74th/sparrow62-buildguide/img/60c/sparrow60c_default_keymap.png

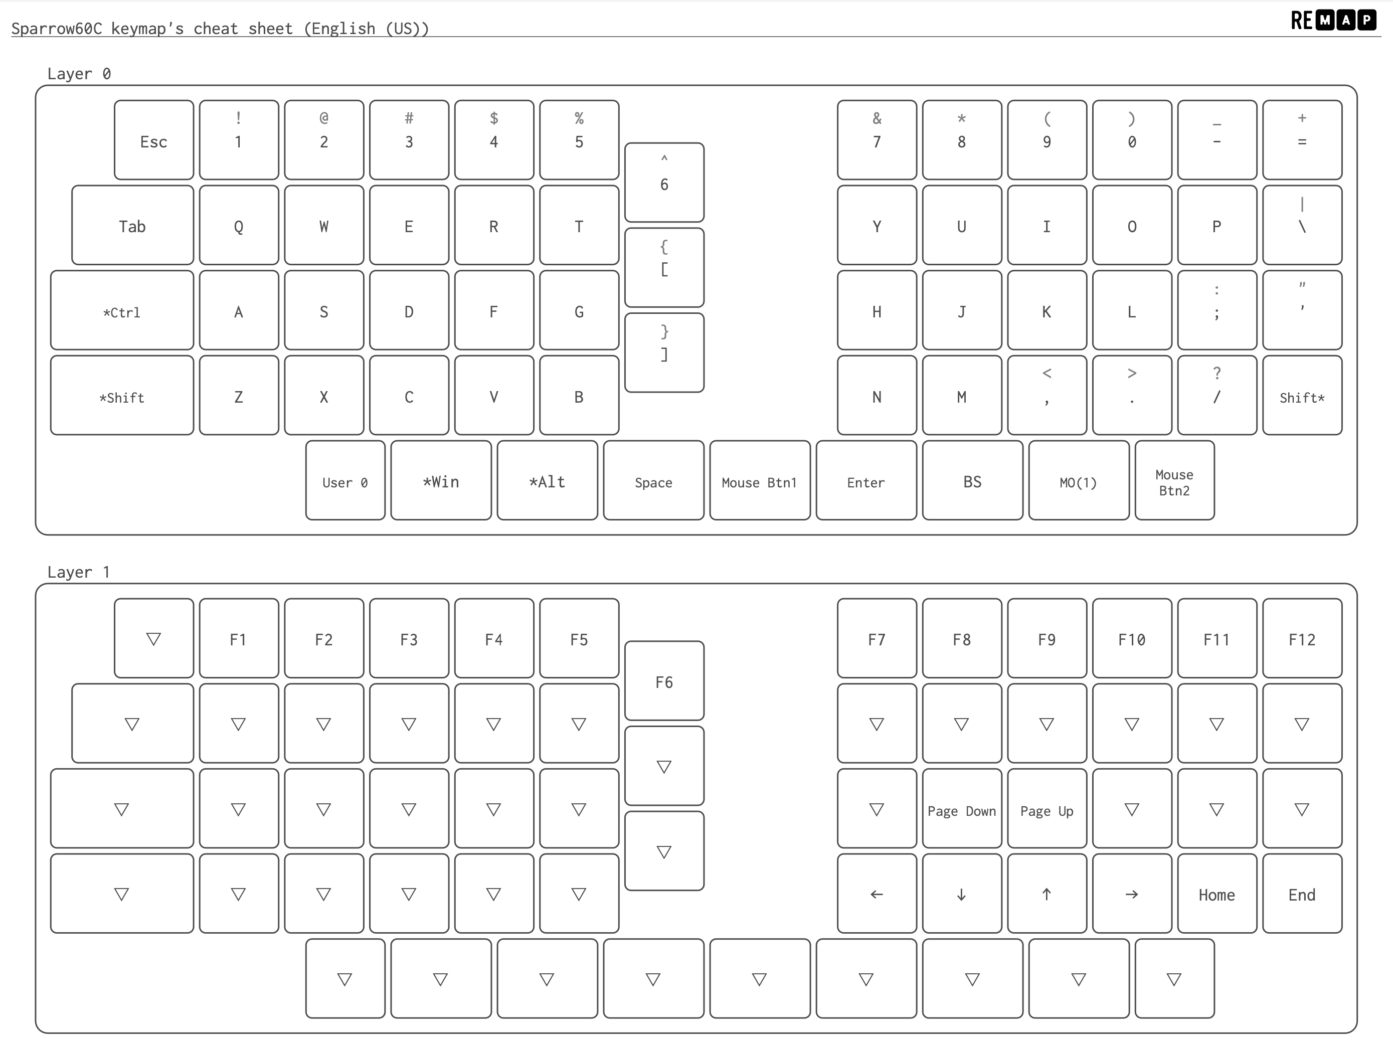
img/60c/sparrow60c_default_keymap.png
