74th/sparrow62-buildguide/img/62v1/diode3.jpg

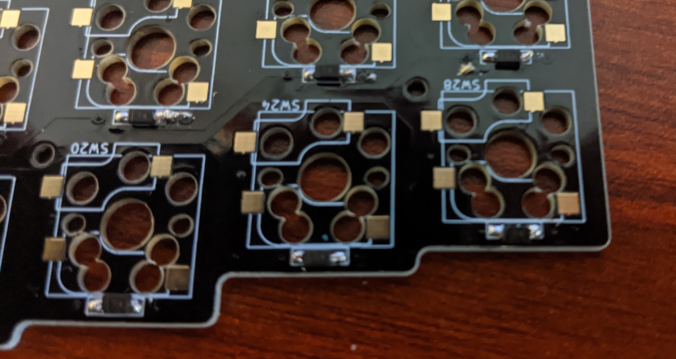
img/62v1/diode3.jpg
