74th/sparrow62-buildguide/img/62v1/keymap_default.png

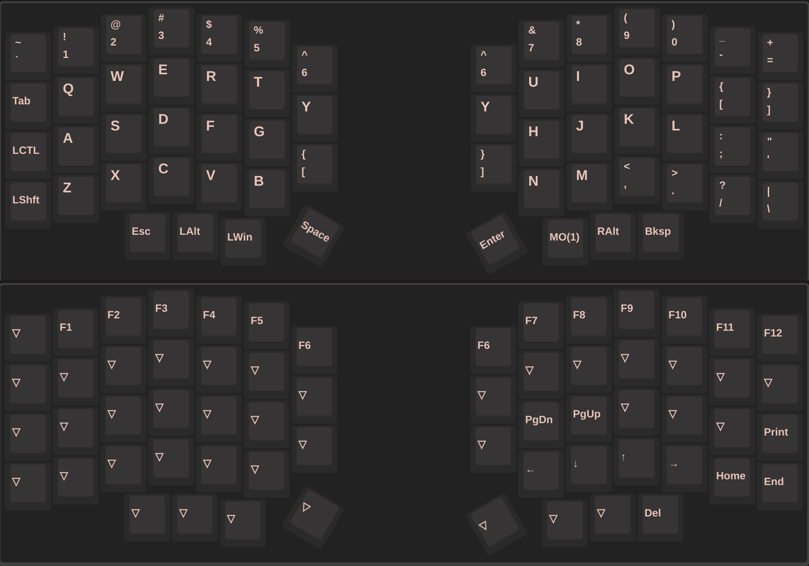
img/62v1/keymap_default.png
