74th/sparrow62-buildguide/img/62v1/pcb.jpg

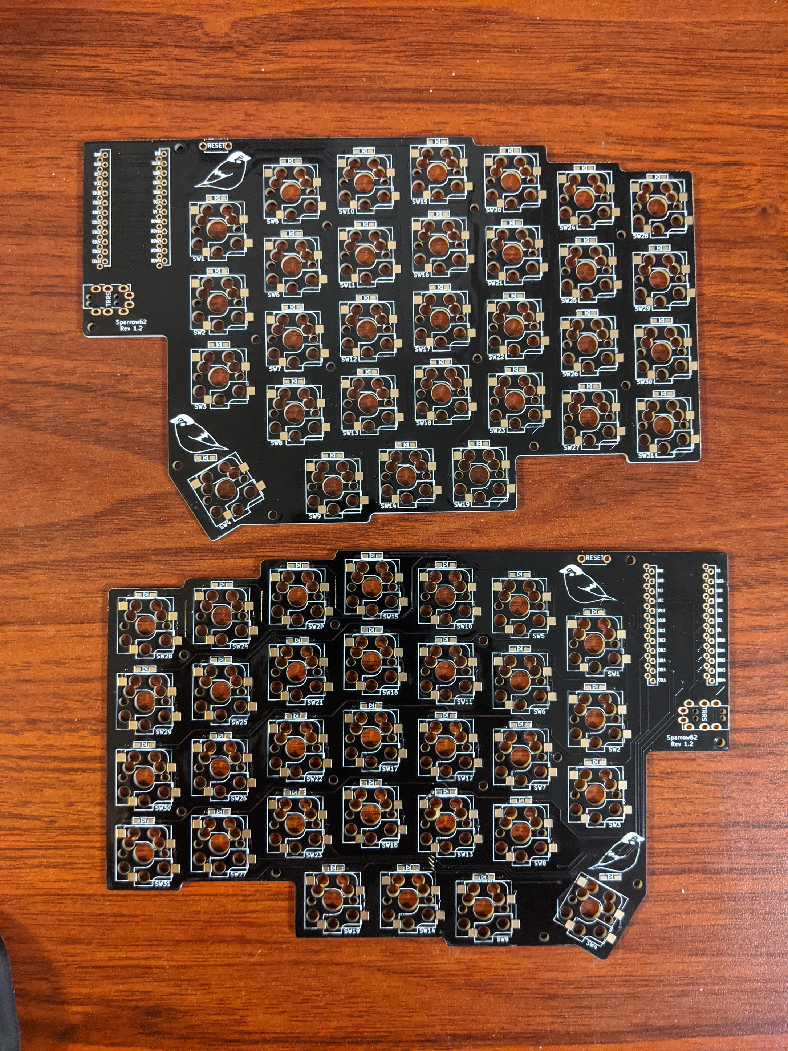
img/62v1/pcb.jpg
