74th/sparrow62-buildguide/img/62v1/top_choc3.jpg

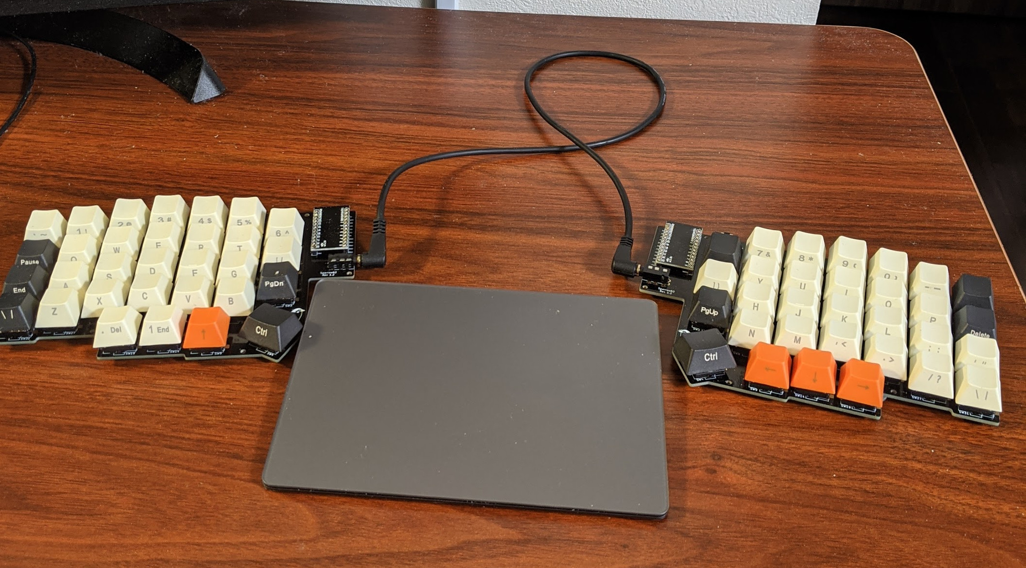
img/62v1/top_choc3.jpg
