74th/sparrow62-buildguide/img/62v1/trackpad.jpeg

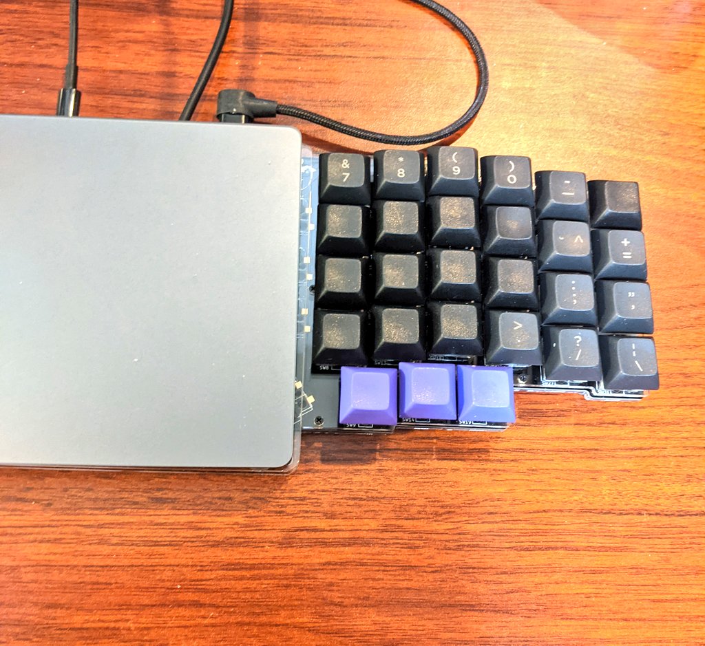
img/62v1/trackpad.jpeg
