74th/sparrow62-buildguide/img/62v2/diode_2.jpg

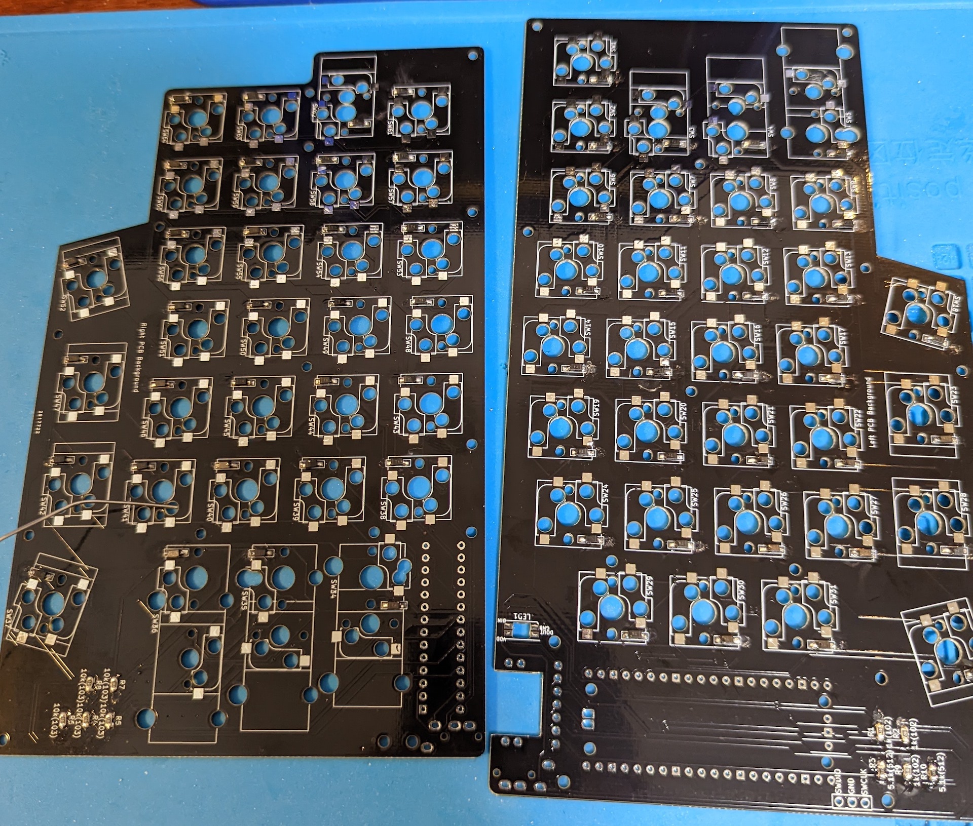
img/62v2/diode_2.jpg
