74th/sparrow62-buildguide/img/62v2/trackpad_option.jpg

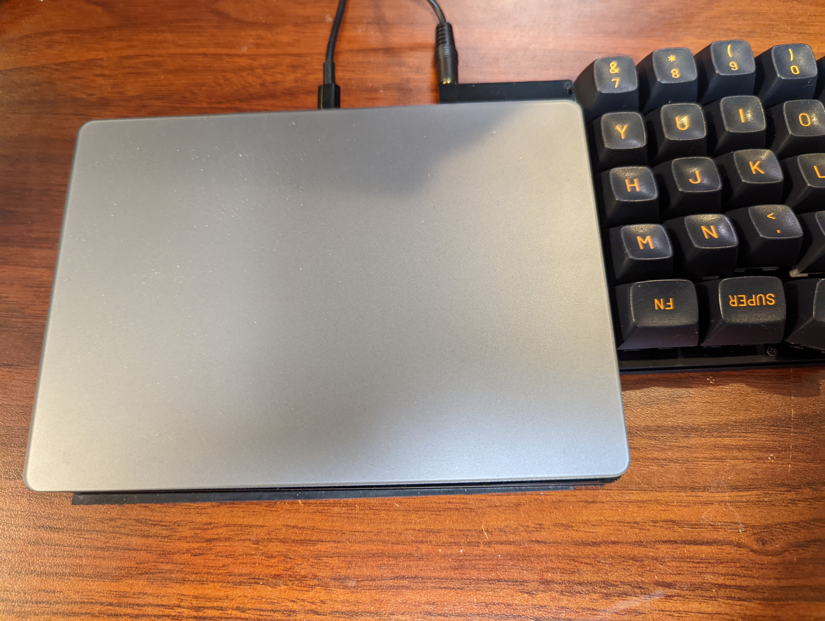
img/62v2/trackpad_option.jpg
