74th/sparrow62-buildguide/img/common/remap_select_usb.png

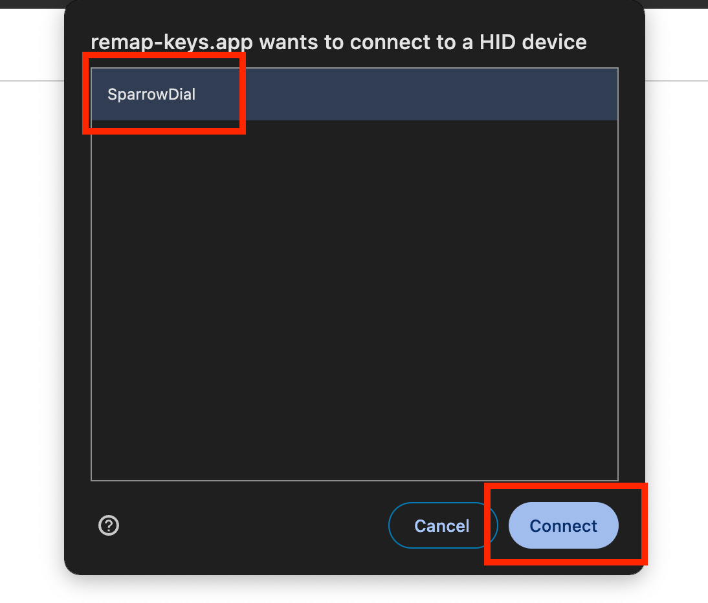
img/common/remap_select_usb.png
