74th/sparrow62-buildguide/img/dial/sparrowdial_default_keymap.png

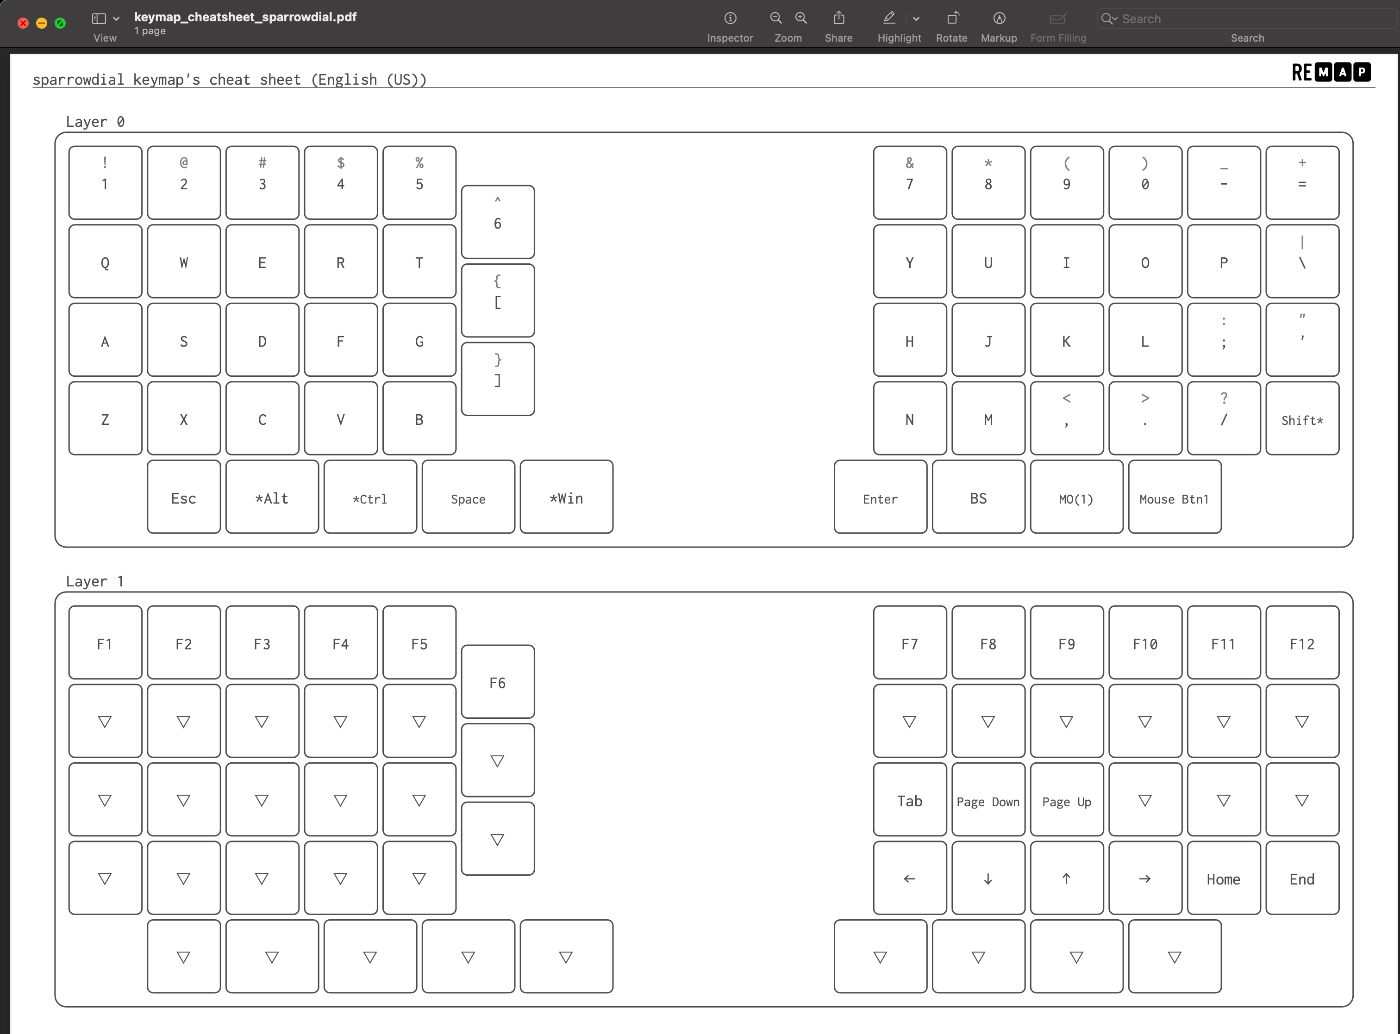
img/dial/sparrowdial_default_keymap.png
