74th/sparrow62-buildguide/img/g21/gp2040-peripheral-mapping.png

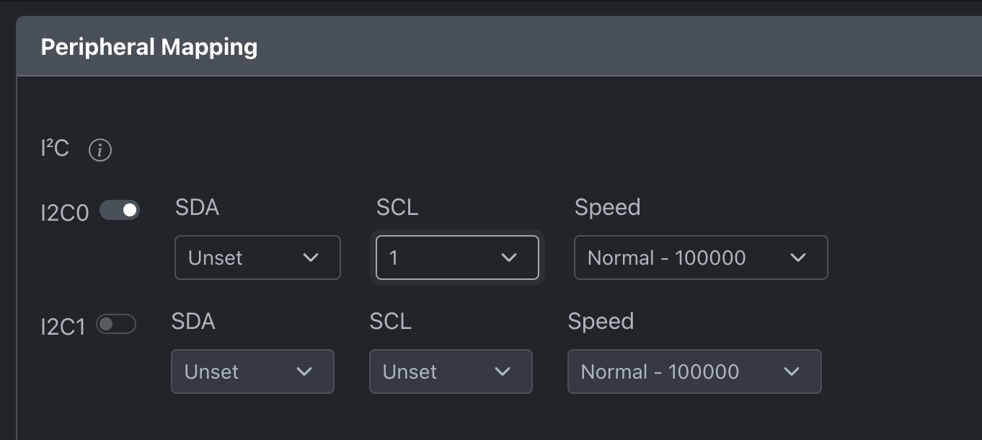
img/g21/gp2040-peripheral-mapping.png
