74th/sparrow62-buildguide/img/g21/gp2040-pin-mapping-v0.7.7.png

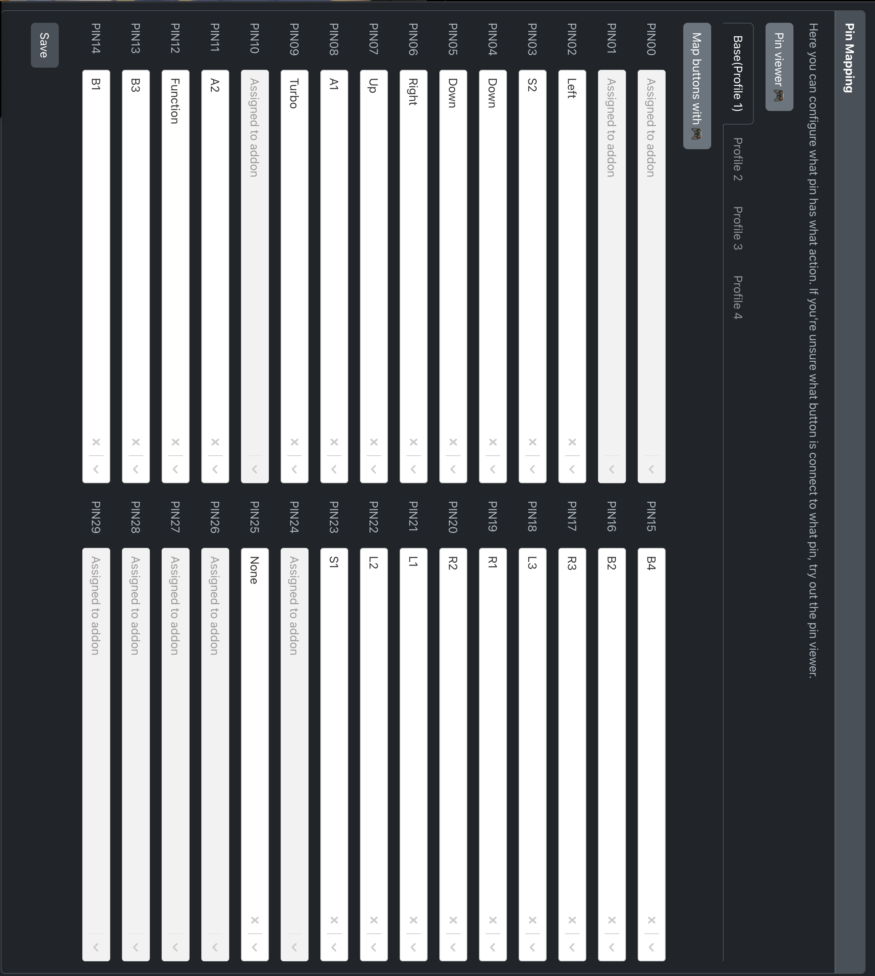
img/g21/gp2040-pin-mapping-v0.7.7.png
