74th/sparrow62-buildguide/img/g21/gp2040-turbo.png

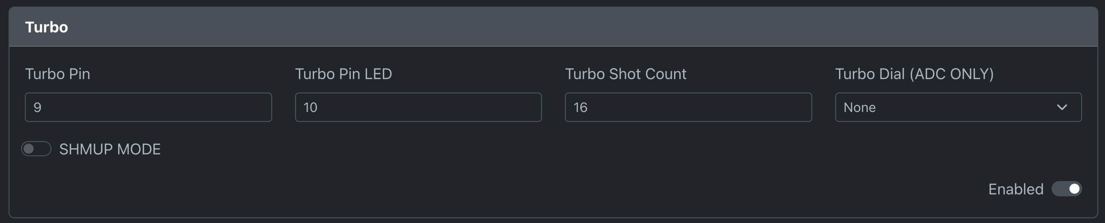
img/g21/gp2040-turbo.png
