74th/sparrow62-buildguide/photos/60c/alminium_case.jpg

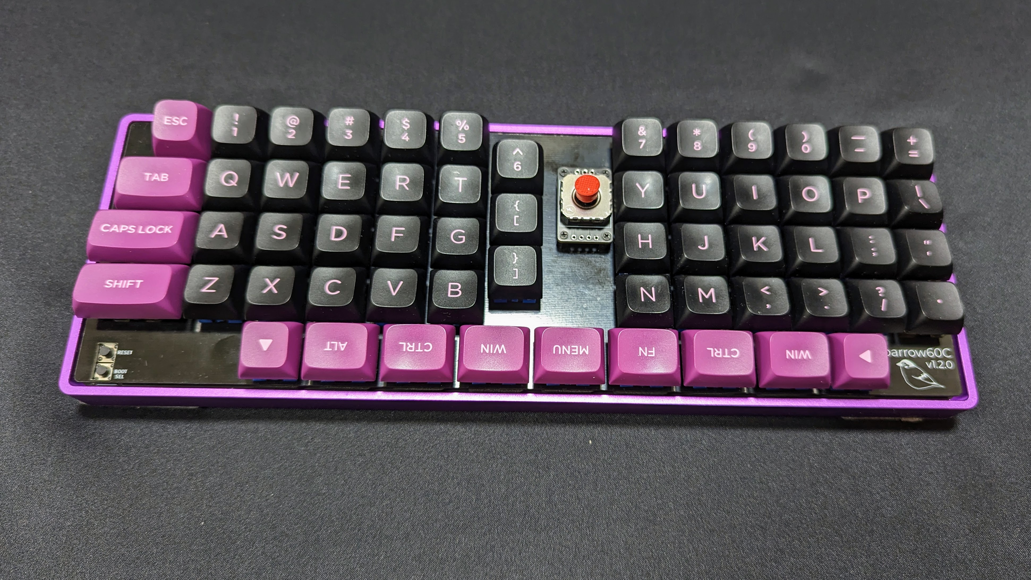
photos/60c/alminium_case.jpg
