74th/sparrow62-buildguide/photos/60c/slide.png

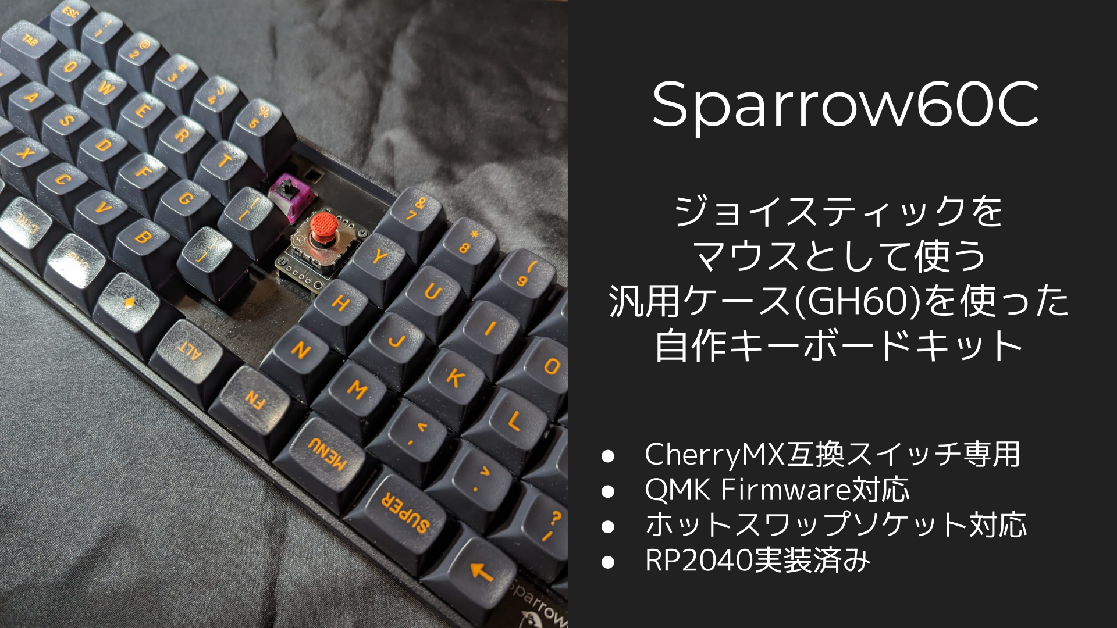
photos/60c/slide.png
