74th/sparrow62-buildguide/photos/60c/stick.jpg

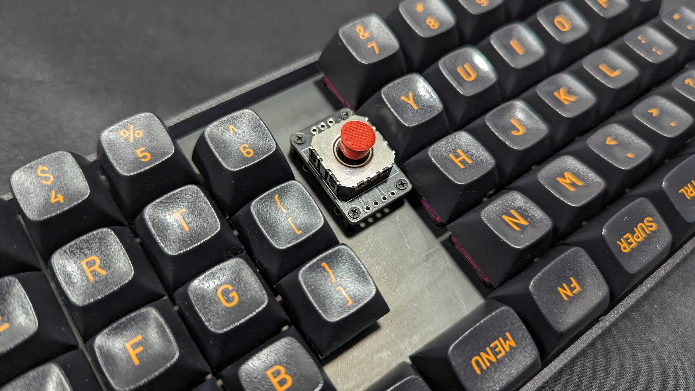
photos/60c/stick.jpg
