74th/sparrow62-buildguide/photos/dial/dial2.jpg

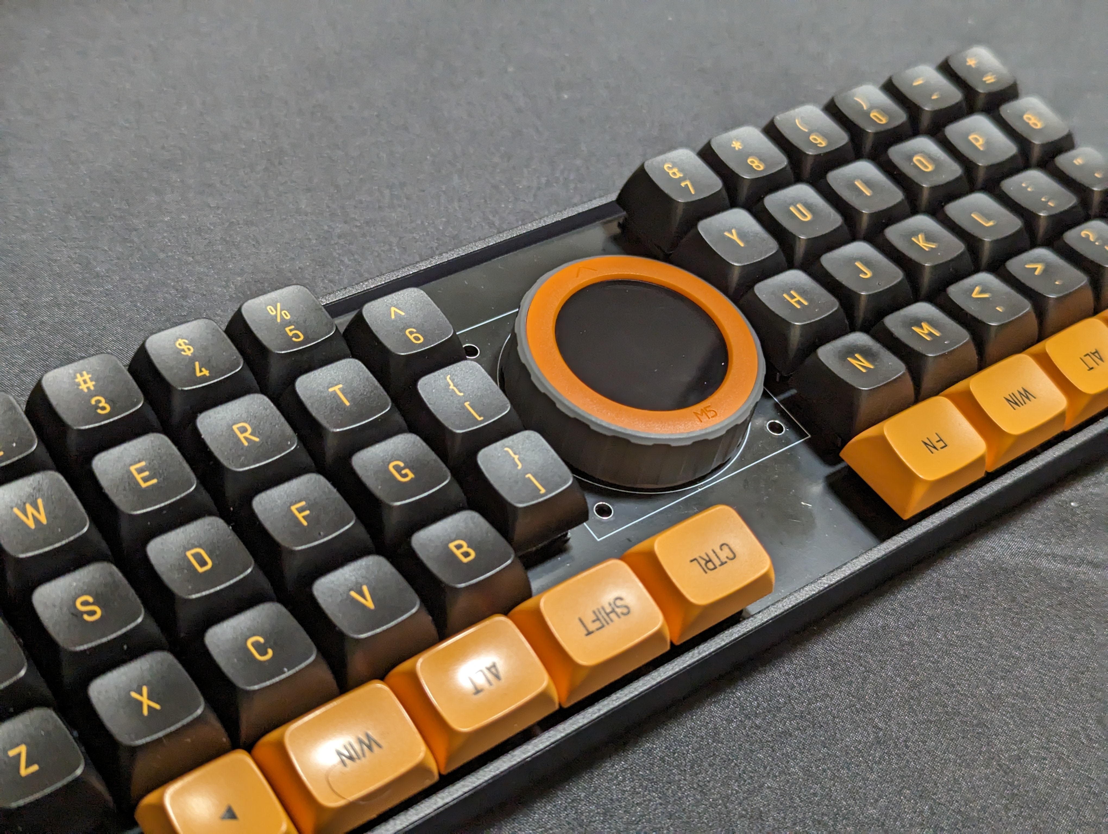
photos/dial/dial2.jpg
