74th/sparrow62-buildguide/photos/dial/dial.jpg

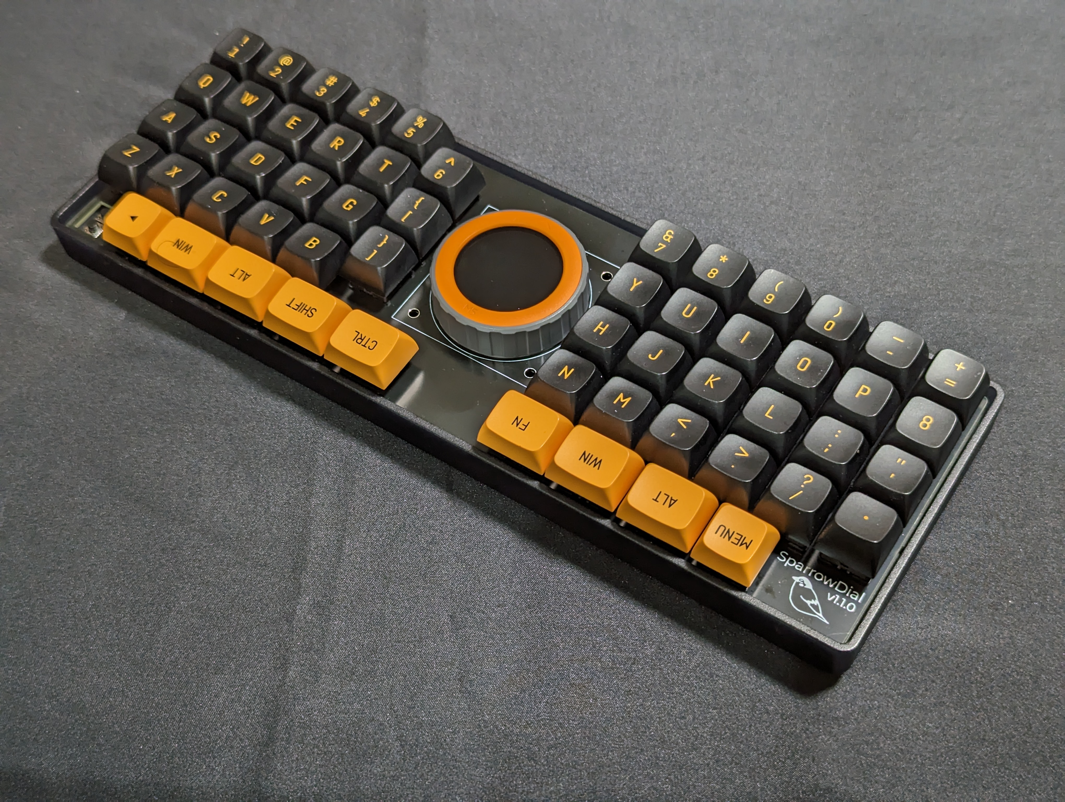
photos/dial/dial.jpg
