74th/sparrow62-buildguide/photos/dial/double.jpg

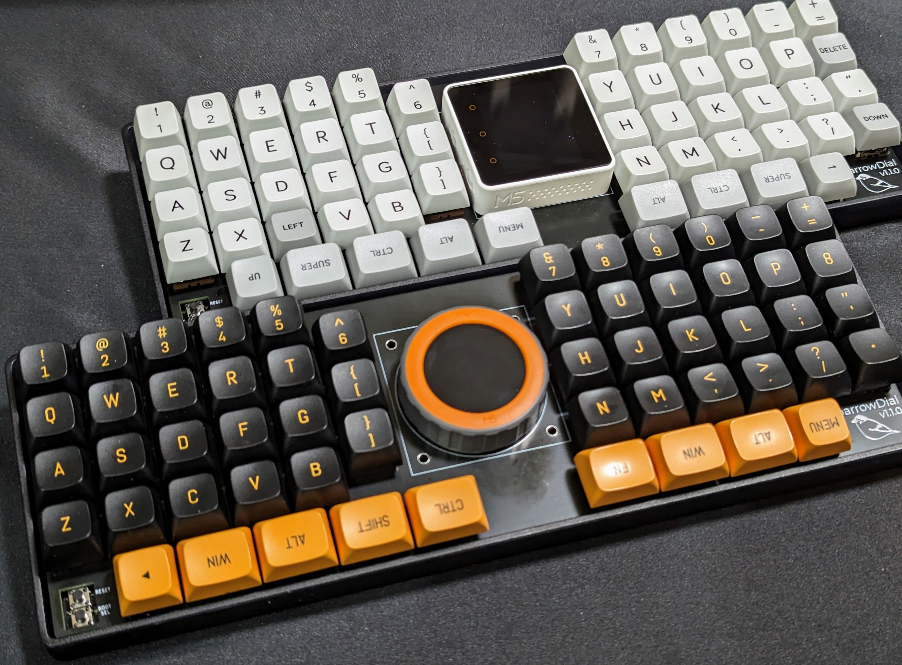
photos/dial/double.jpg
