74th/sparrow62-buildguide/photos/dial/stack2.jpg

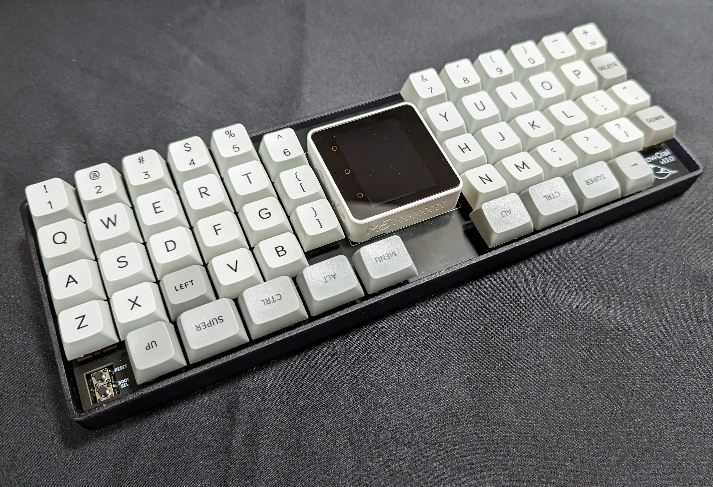
photos/dial/stack2.jpg
