74th/sparrow62-buildguide/photos/dial/stack.jpg

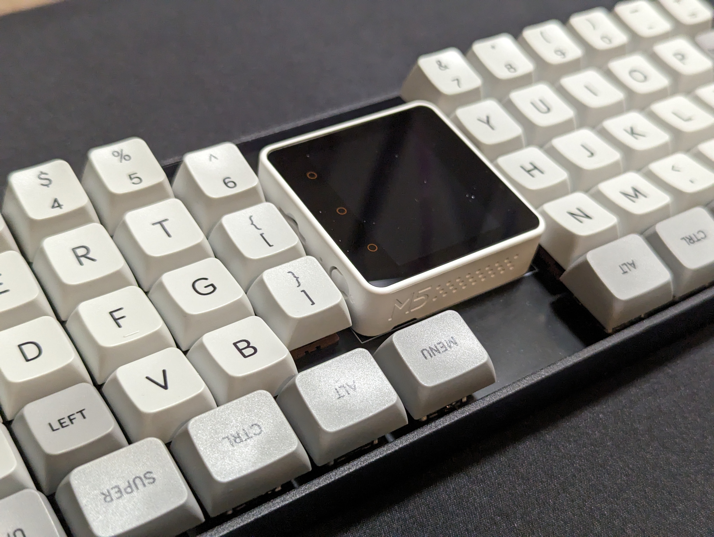
photos/dial/stack.jpg
