74th/sparrow62-buildguide/photos/g21/hollowknight.png

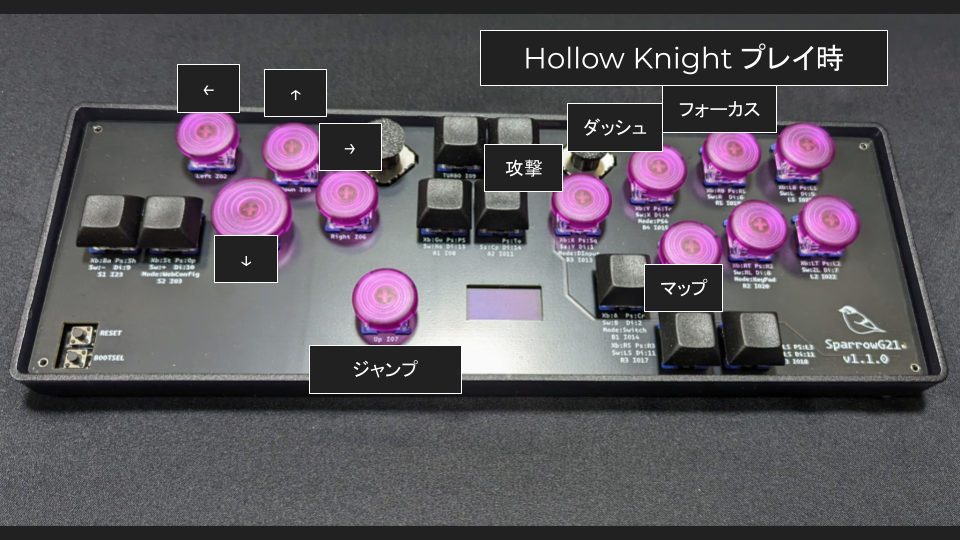
photos/g21/hollowknight.png
