74th/sparrow62-buildguide/photos/g21/joystick.jpg

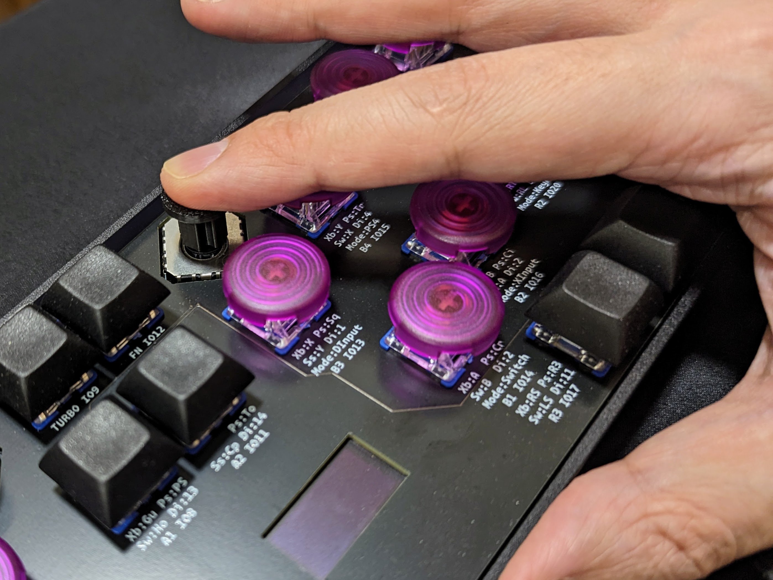
photos/g21/joystick.jpg
