74th/sparrow62-buildguide/photos/g21/left.jpg

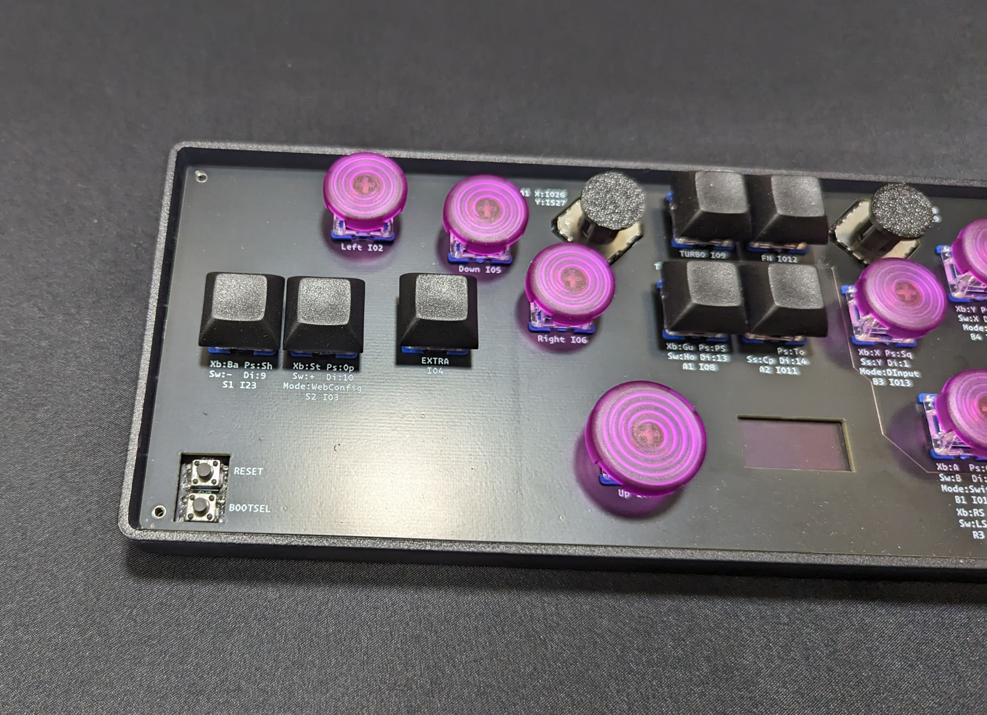
photos/g21/left.jpg
