74th/sparrow62-buildguide/photos/g21/overview.jpg

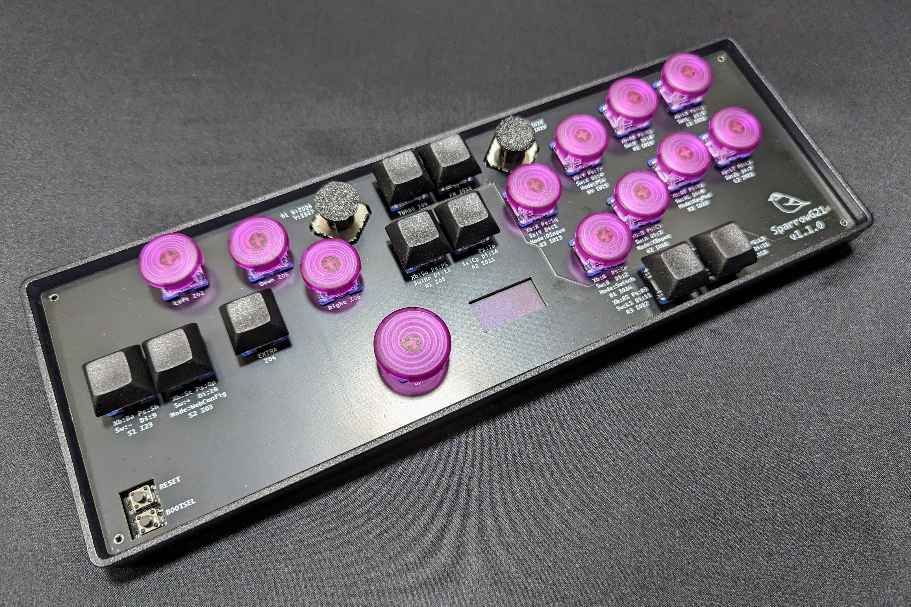
photos/g21/overview.jpg
