74th/sparrow62-buildguide/photos/g21/right.jpg

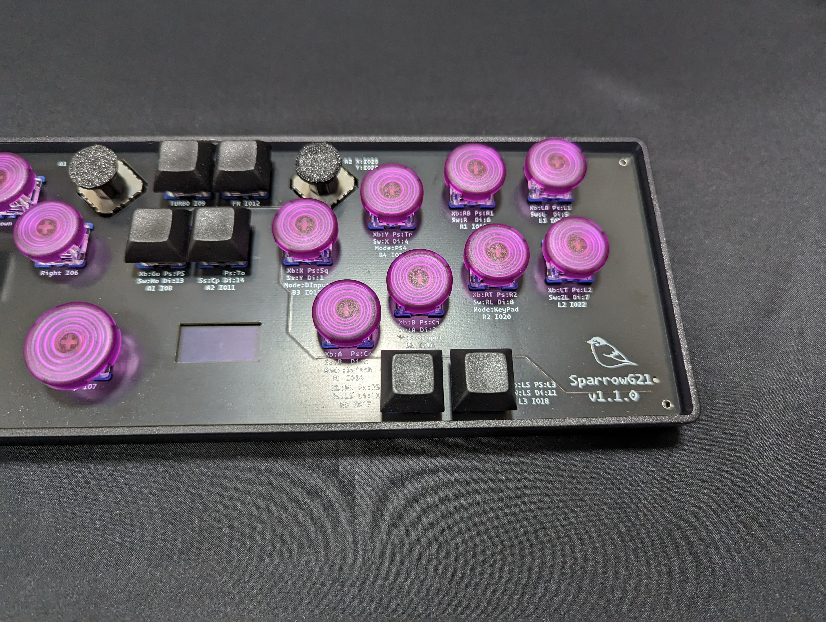
photos/g21/right.jpg
