74th/sparrow62-buildguide/photos/g21/slide.png

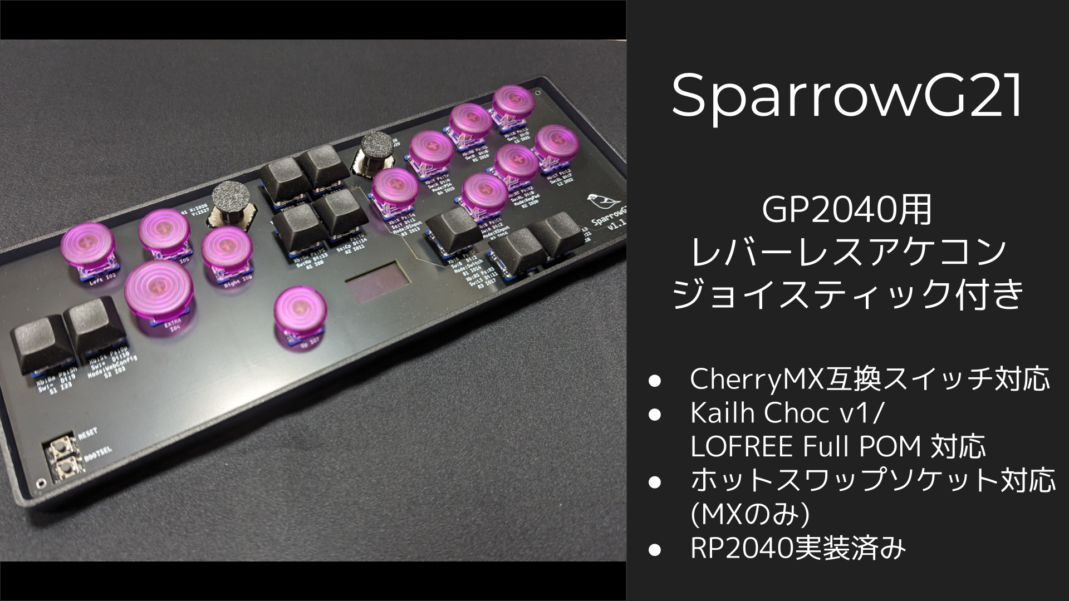
photos/g21/slide.png
