74th/sparrow62-buildguide/photos/tv/top.jpg

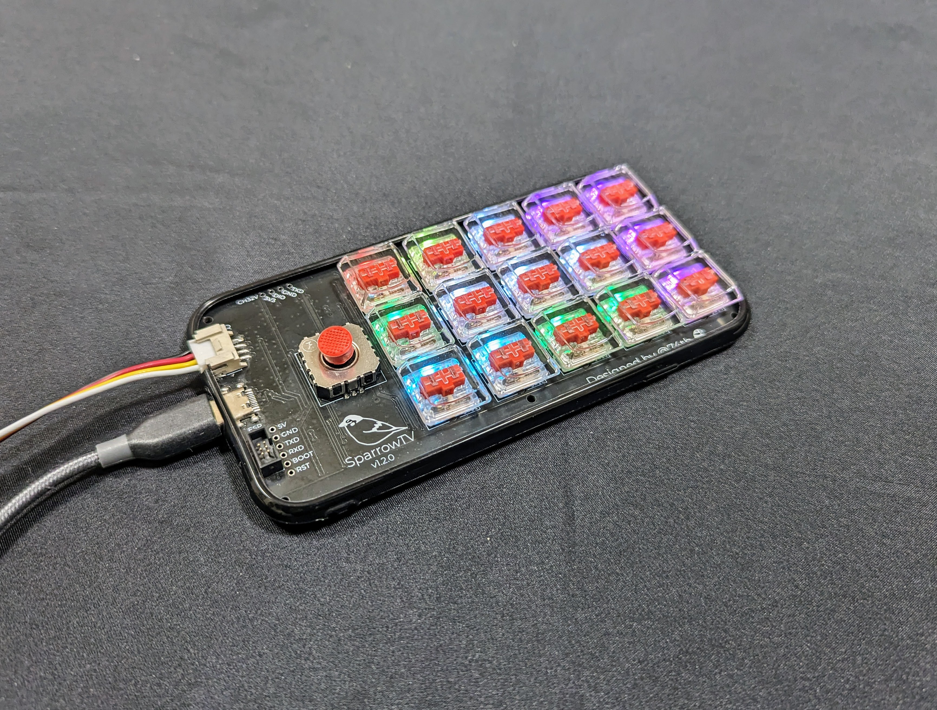
photos/tv/top.jpg
