74th/sparrow62-buildguide/photos/v2/left.jpg

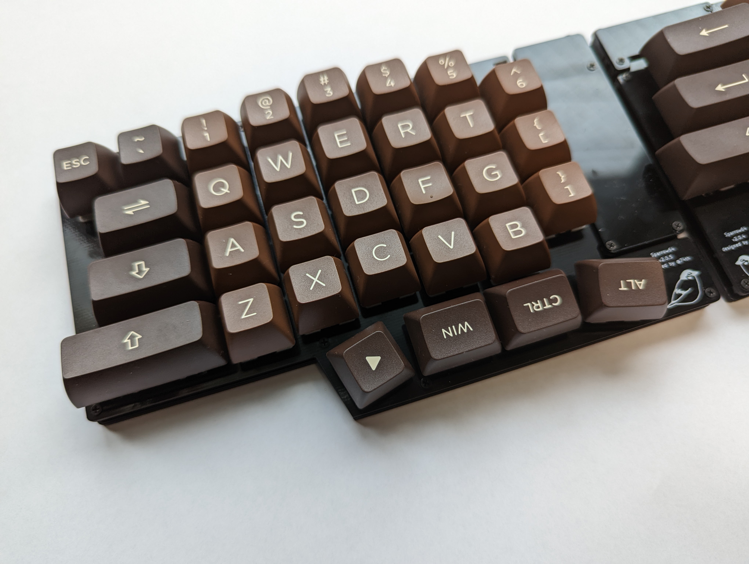
photos/v2/left.jpg
