74th/sparrow62-buildguide/photos/v2/lower.png

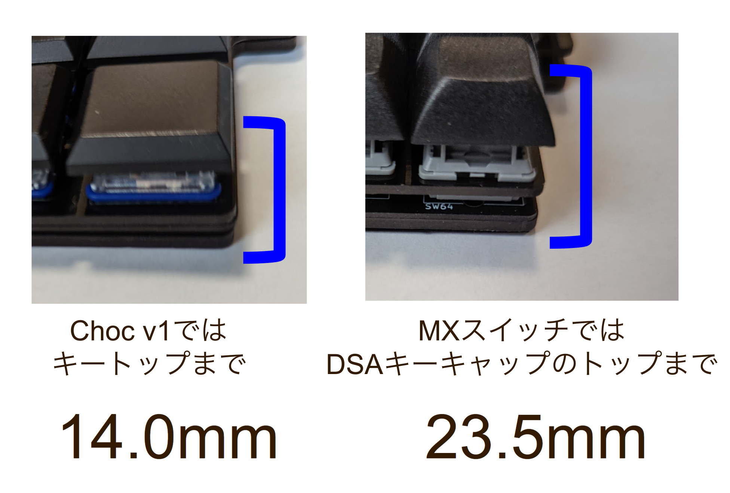
photos/v2/lower.png
