74th/sparrow62-buildguide/photos/v2/plate-back.jpg

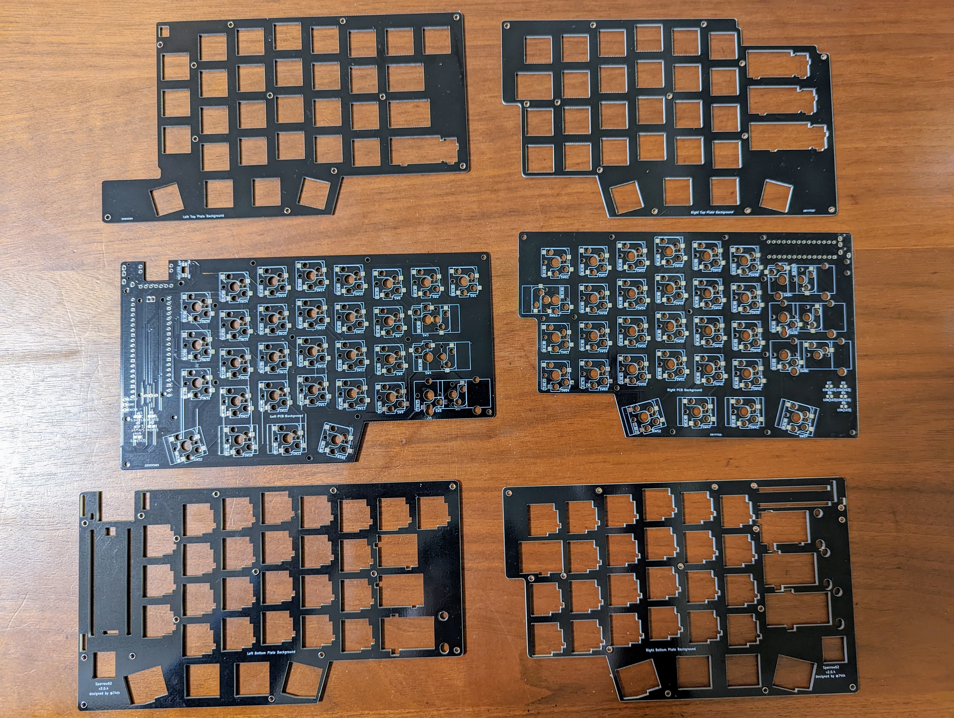
photos/v2/plate-back.jpg
