74th/sparrow62-buildguide/photos/v2/plate-front.jpg

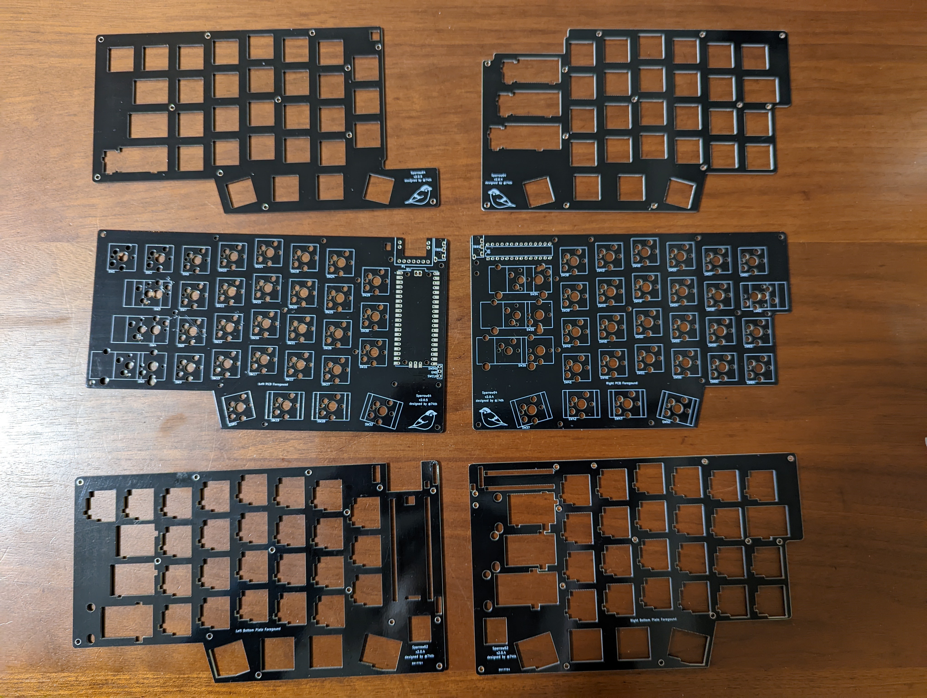
photos/v2/plate-front.jpg
