74th/sparrow62-buildguide/photos/v2/right.jpg

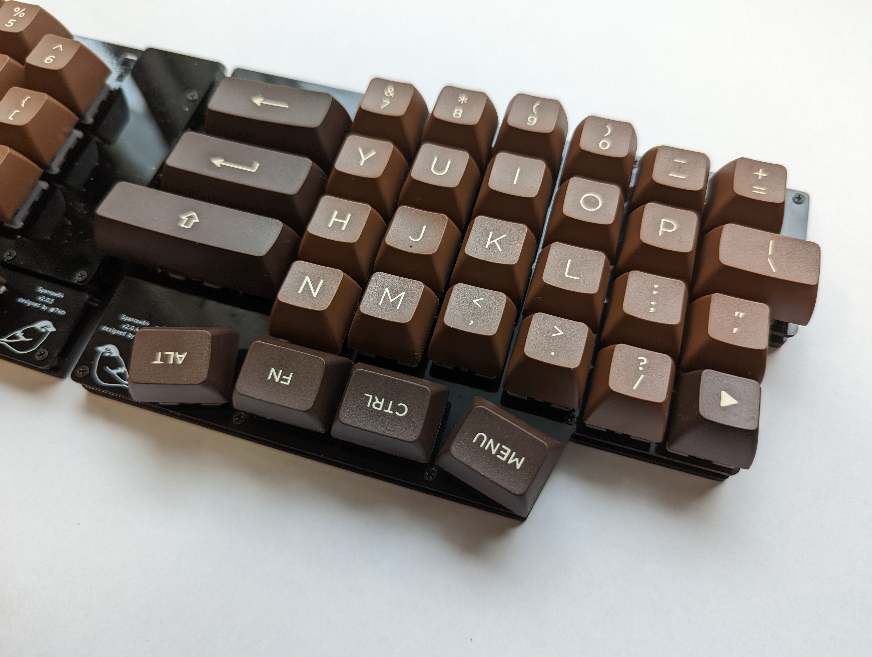
photos/v2/right.jpg
