74th/sparrow62-buildguide/photos/v2/trackpad-option.jpg

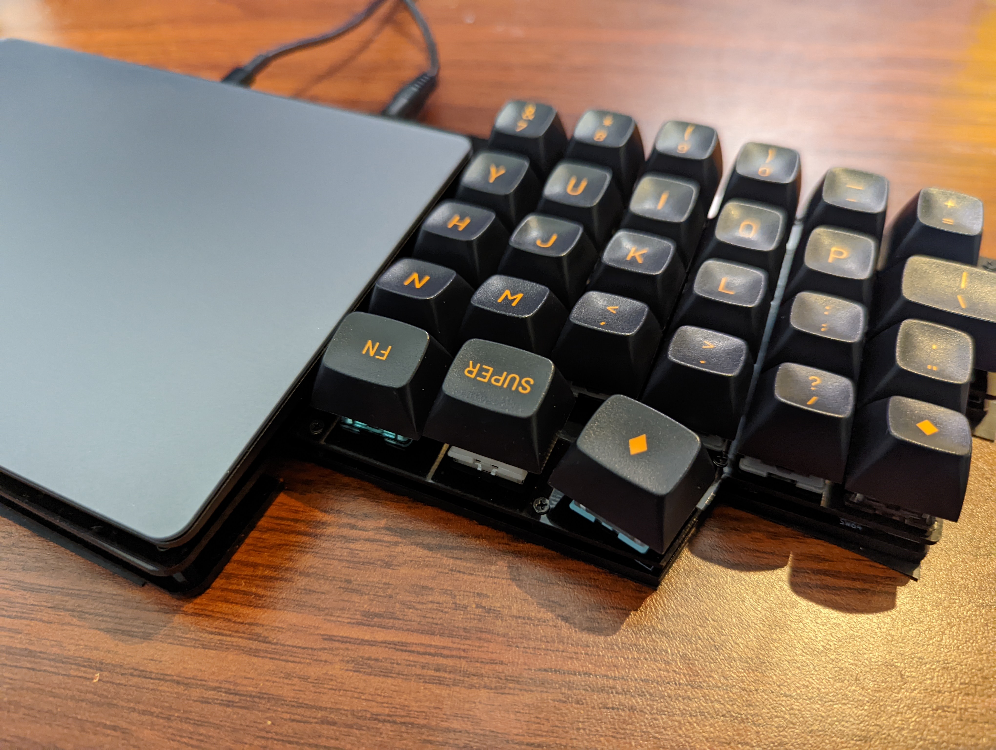
photos/v2/trackpad-option.jpg
