74th/sparrow62-buildguide/photos/v2/zoom.jpeg

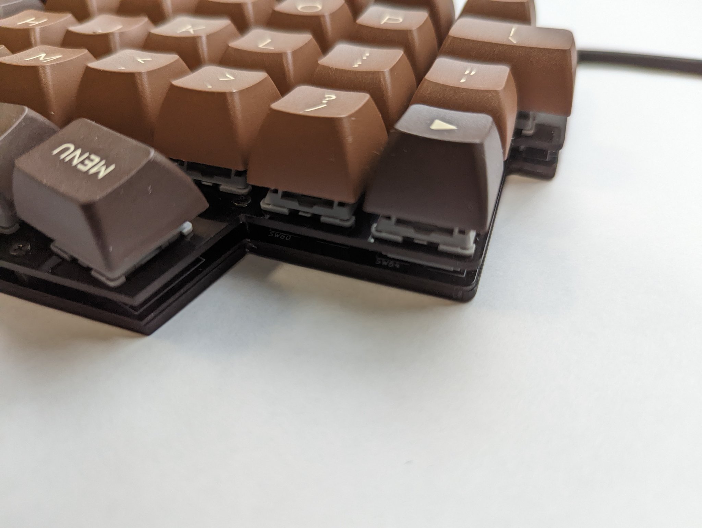
photos/v2/zoom.jpeg
