74th/sparrow62-buildguide/photos/v2/zoom.jpg

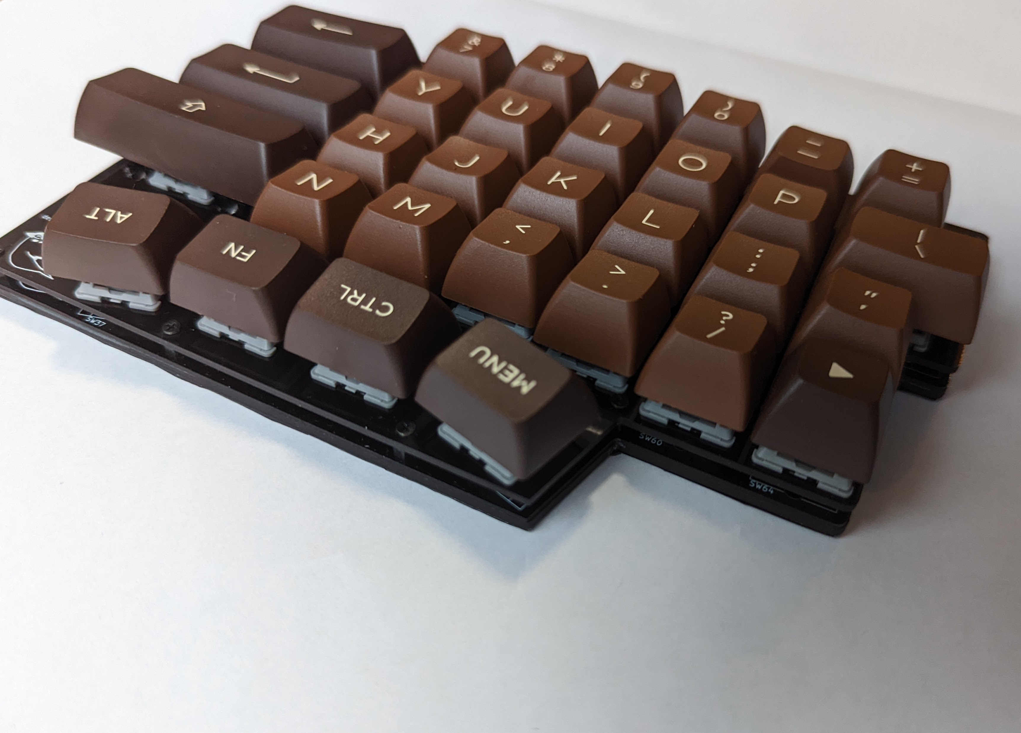
photos/v2/zoom.jpg
