74th/sparrow62-buildguide/photos/v2/parts.jpg

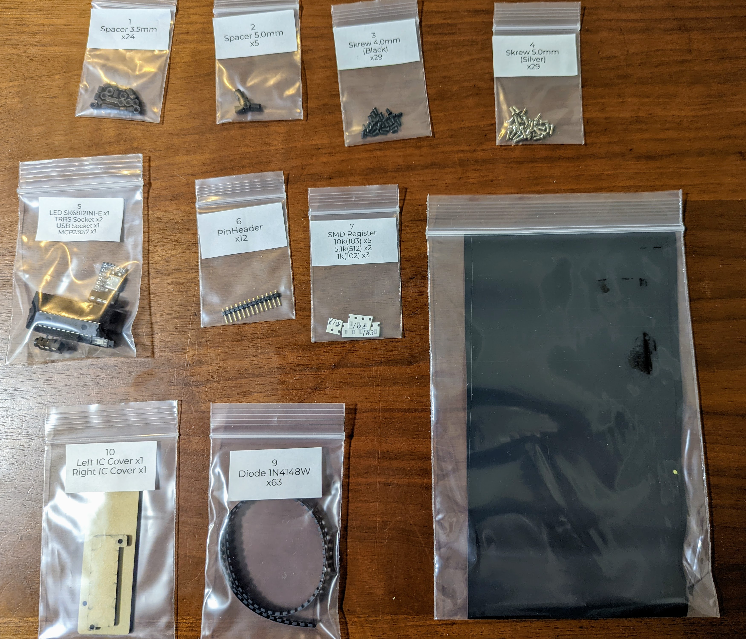
photos/v2/parts.jpg
